pdx-lutter/pdx-ece411-fall2018-kjn/docs/data-sheets/ds1621_i2c_waveforms.png

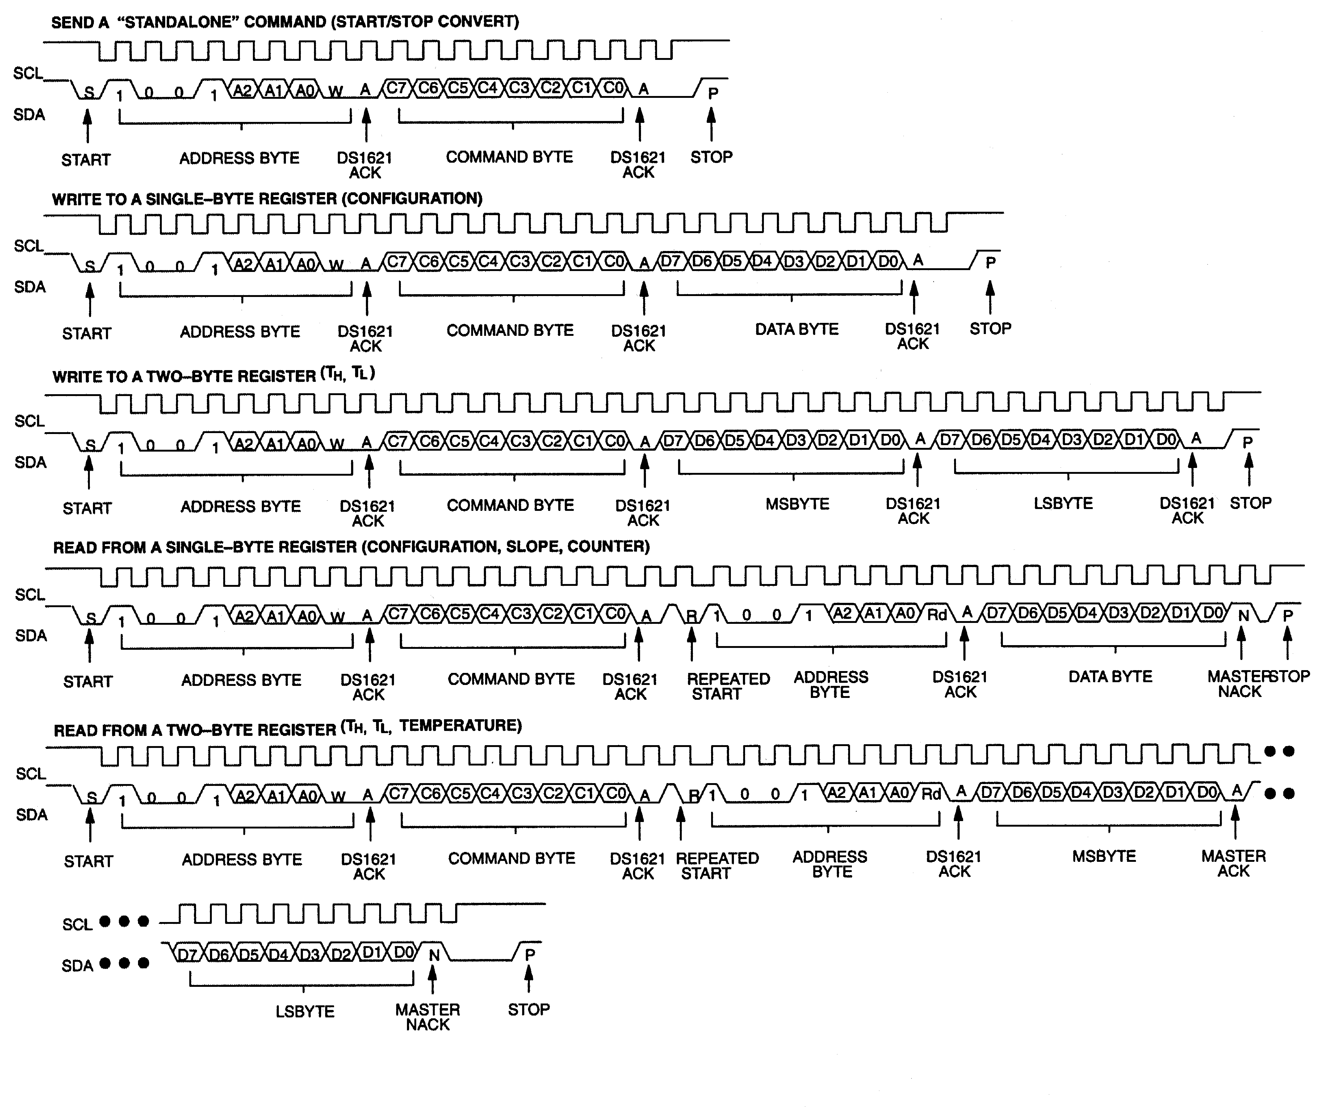
docs/data-sheets/ds1621_i2c_waveforms.png
