pdx-lutter/pdx-ece411-fall2018-kjn/docs/data-sheets/qianji_JQC-3F-relay.jpg

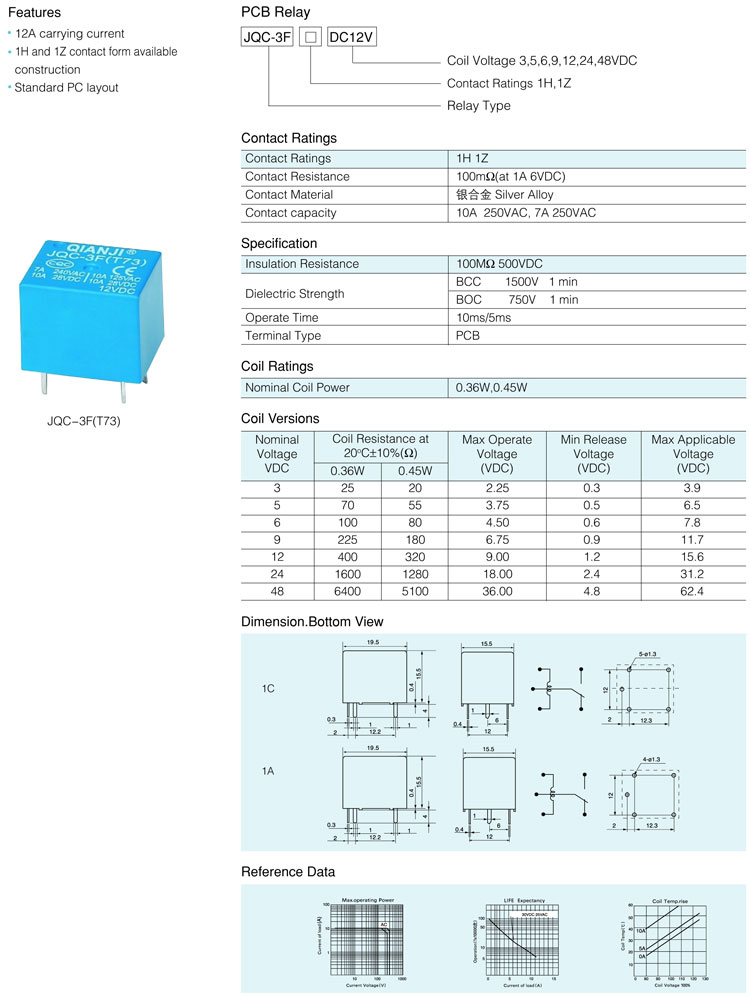
docs/data-sheets/qianji_JQC-3F-relay.jpg
