pdx-lutter/pdx-ece411-fall2018-kjn/docs/Schematics and Board designs/images/ECE411_G16_UIV1_BRD.png

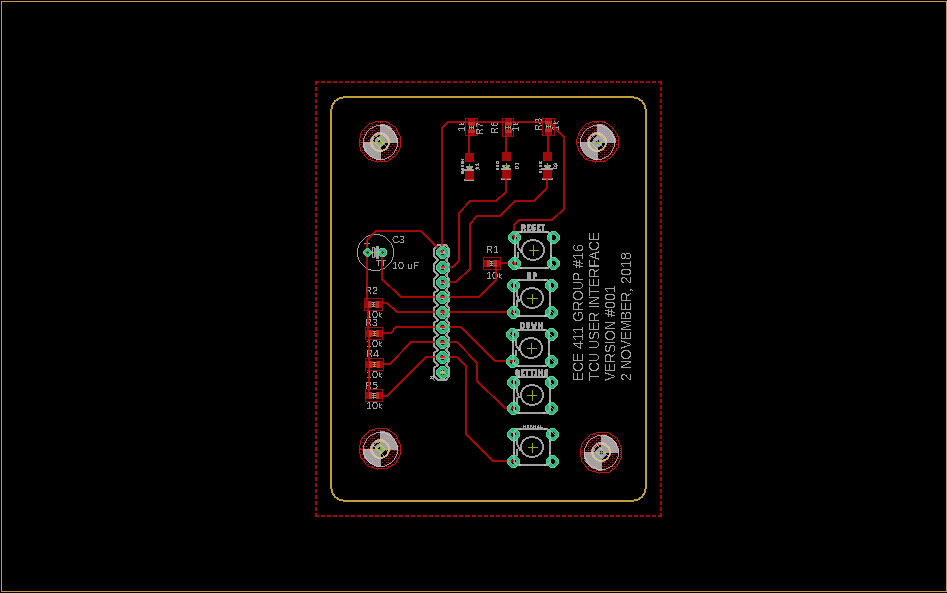
docs/Schematics and Board designs/images/ECE411_G16_UIV1_BRD.png
