pdx-lutter/pdx-ece411-fall2018-kjn/docs/Schematics and Board designs/images/ECE411_G16_V6_BRD.png

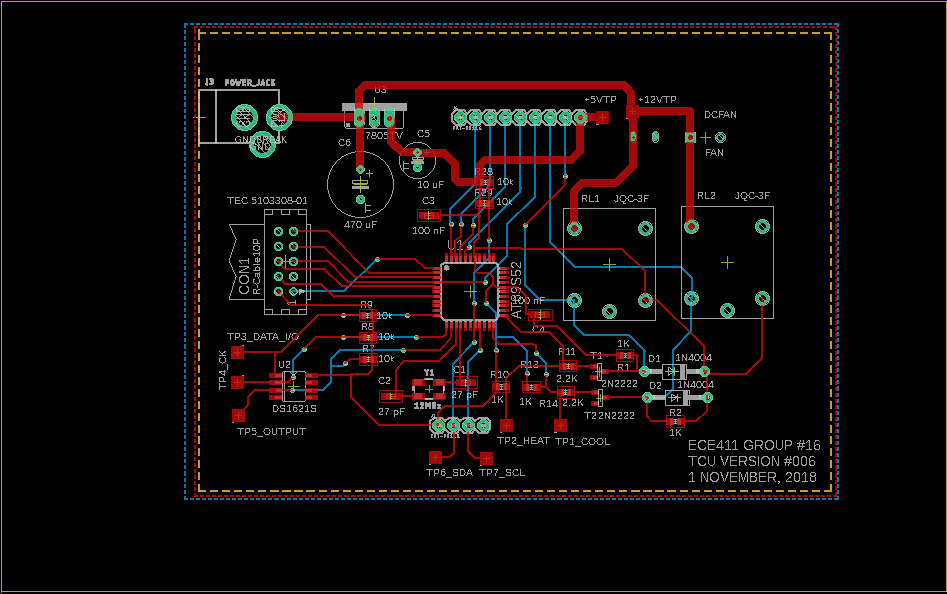
docs/Schematics and Board designs/images/ECE411_G16_V6_BRD.png
